Tinamous/JediLightSwitch/V1.1/Enclosure/Cover-28mm-V1.1.stl

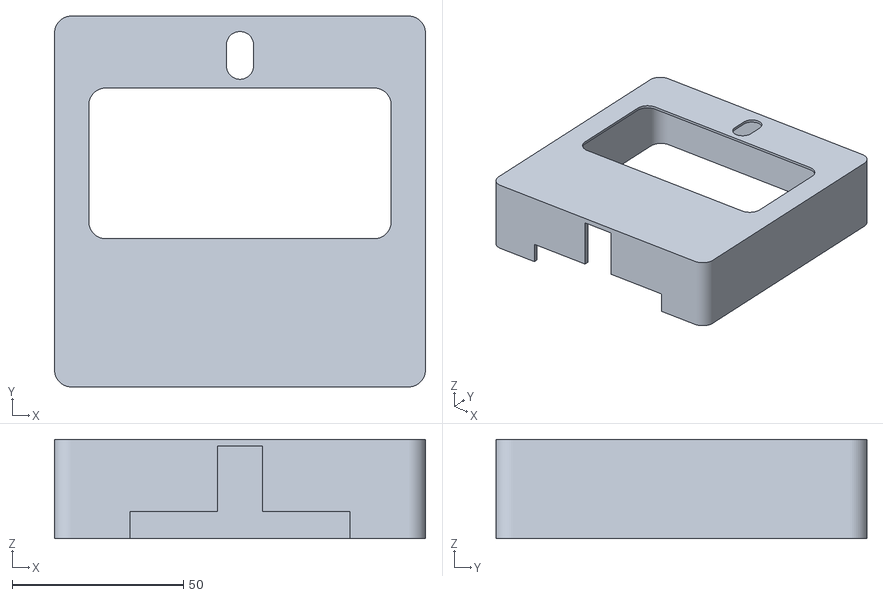
[picture p17: CAD file, 2016-02-15, an earlier design]
V1.1/Enclosure/Cover-28mm-V1.1.stl
108.2 x 108.2 x 29.0
