Tinamous/JediLightSwitch/V1.1/Enclosure/Cover-25mm-V1.2.stl

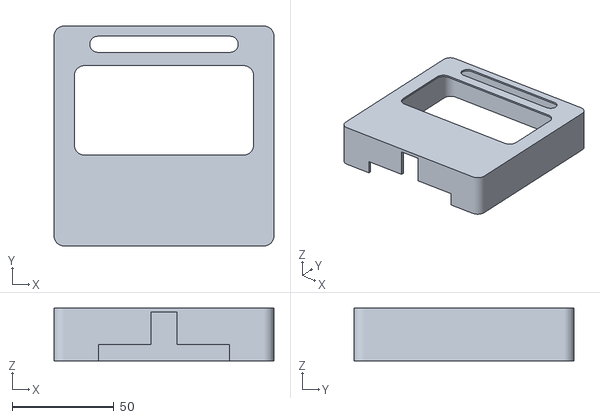
[picture p18: CAD file, 2016-02-15, an earlier design]
V1.1/Enclosure/Cover-25mm-V1.2.stl
108.2 x 108.2 x 26.0
